schemen/OpenFormicaria/Formicaria/Inserts/Lasius_size_m.png

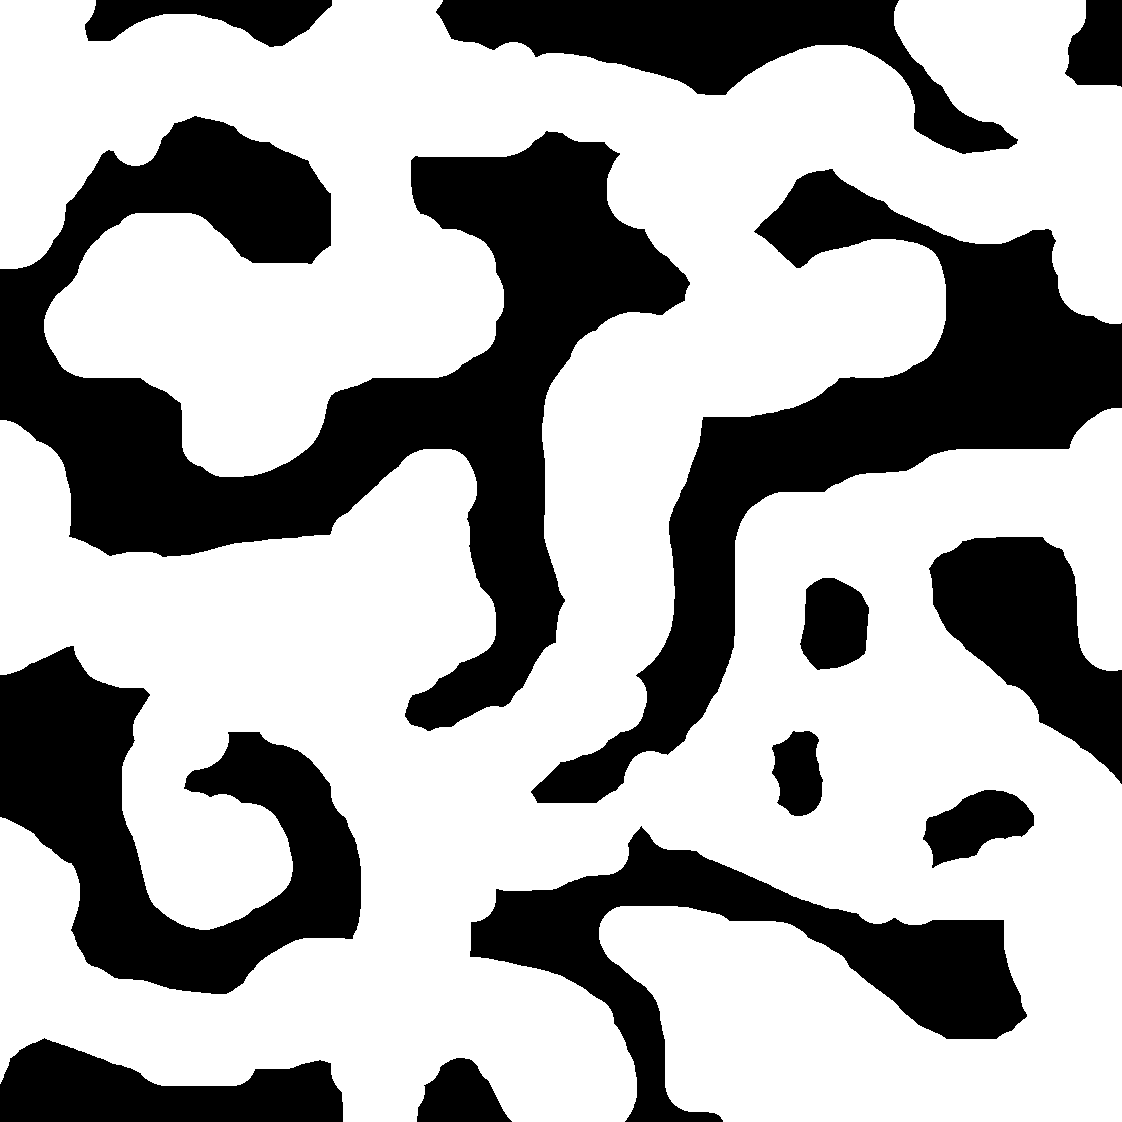
Formicaria/Inserts/Lasius_size_m.png
