schemen/OpenFormicaria/Formicaria/Inserts/Lasius_size_s.png

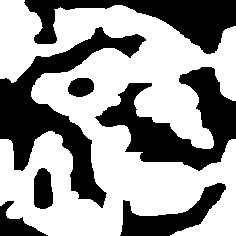
Formicaria/Inserts/Lasius_size_s.png
