schemen/OpenFormicaria/Modules/CAD/CV1/4xGateway.FCStd

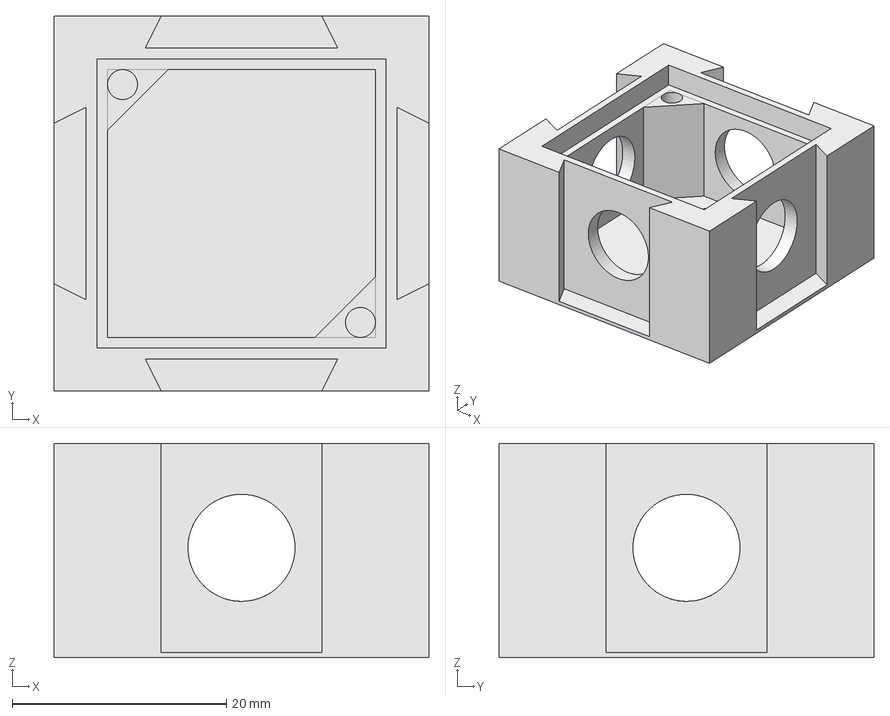
[picture p29: CAD file, 2020-11-02]
Modules/CAD/CV1/4xGateway.FCStd
35.0 x 35.0 x 20.0 mm
