schemen/OpenFormicaria/Modules/CAD/CV2/CV2_4xGateway.FCStd

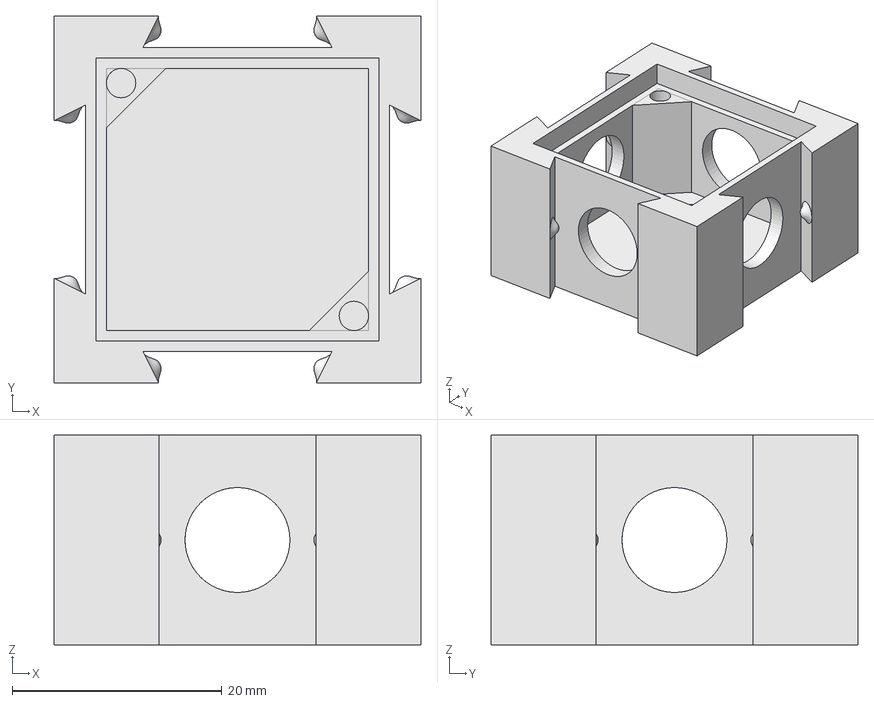
[picture p30: CAD file, 2020-11-02]
Modules/CAD/CV2/CV2_4xGateway.FCStd
35.0 x 35.0 x 20.0 mm
