schemen/OpenFormicaria/Modules/CAD/Portal_FeederLid.FCStd

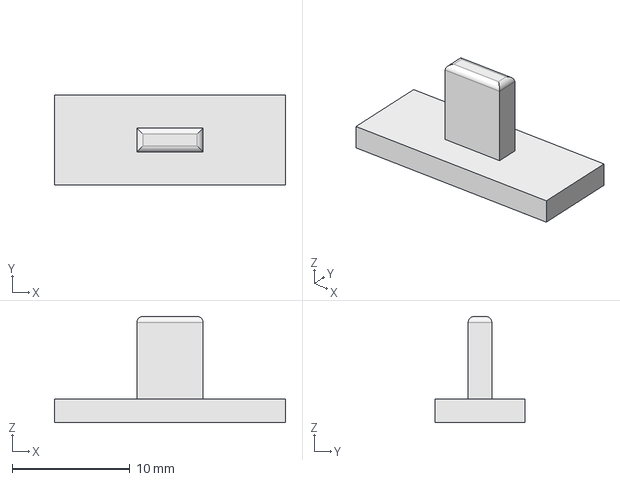
[picture p31: CAD file, 2020-10-29]
Modules/CAD/Portal_FeederLid.FCStd
19.6 x 7.60 x 9.00 mm
