schemen/OpenFormicaria/Connectors/CAD/Connector Version 2/V2_Connector_90deg_tube_12mm.FCStd

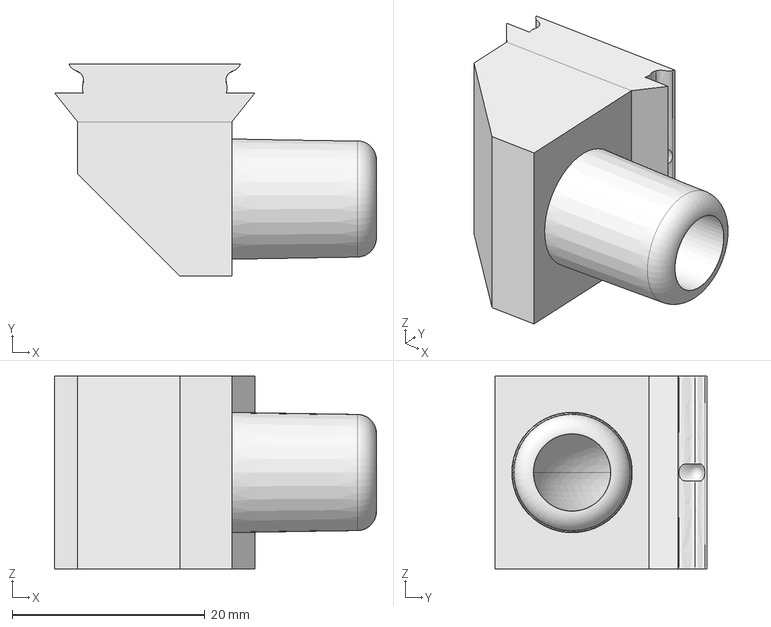
[picture p32: CAD file, 2020-11-05]
Connectors/CAD/Connector Version 2/V2_Connector_90deg_tube_12mm.FCStd
33.4 x 22.0 x 20.0 mm
