schemen/OpenFormicaria/Formicaria/CAD/Formicarium_Lid_S.FCStd

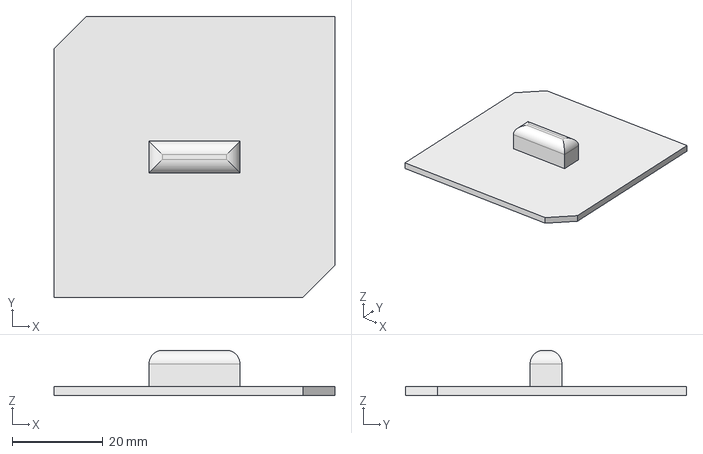
[picture p33: CAD file, 2020-11-02]
Formicaria/CAD/Formicarium_Lid_S.FCStd
61.8 x 61.8 x 10.0 mm
