schemen/OpenFormicaria/Formicaria/STL/CV1/OF_Formicarium_Lasius_M.stl

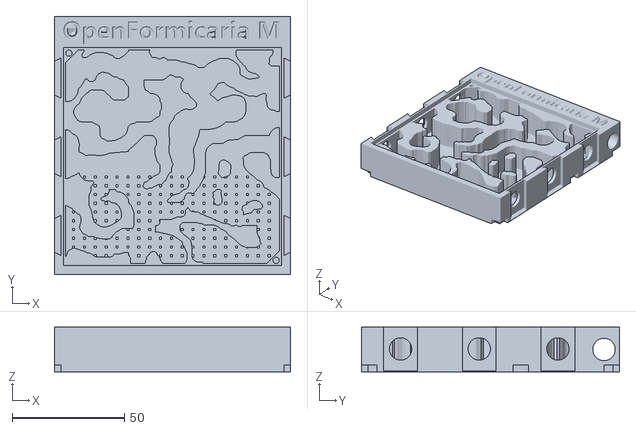
[picture p34: CAD file, 2020-11-02]
Formicaria/STL/CV1/OF_Formicarium_Lasius_M.stl
105.0 x 115.0 x 20.0
