schemen/OpenFormicaria/Formicaria/STL/CV2/CV2_OF_Formicarium_Lasius_S.stl

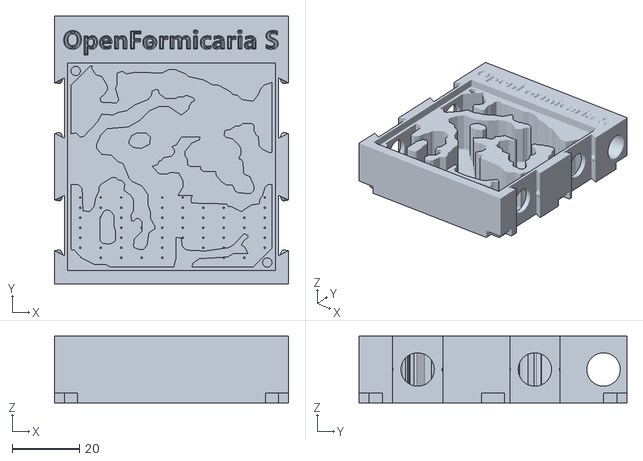
[picture p35: CAD file, 2020-11-05]
Formicaria/STL/CV2/CV2_OF_Formicarium_Lasius_S.stl
70.0 x 80.0 x 20.0
