schemen/OpenFormicaria/Modules/CAD/CV1/Portal.FCStd

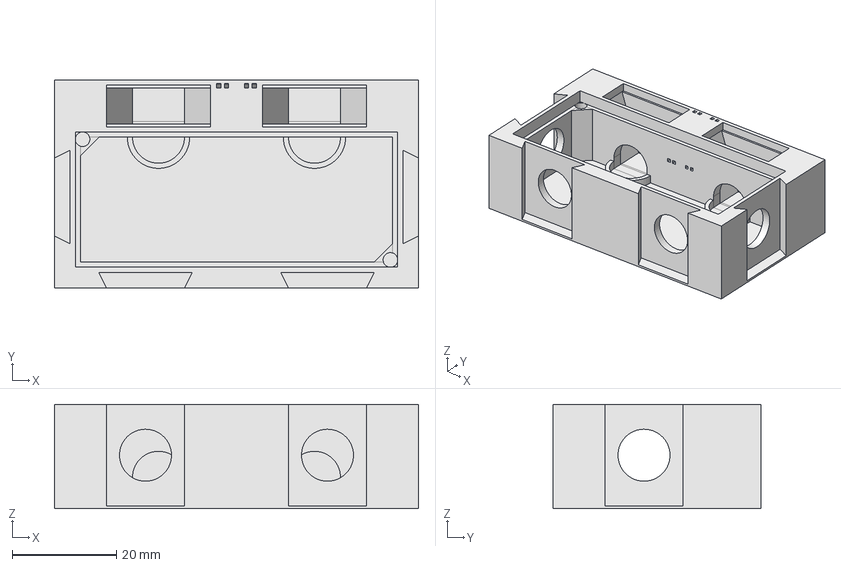
[picture p36: CAD file, 2020-10-29]
Modules/CAD/CV1/Portal.FCStd
70.0 x 40.0 x 20.0 mm
