schemen/OpenFormicaria/Connectors/CAD/Connector Version 2/V2_Connector.FCStd

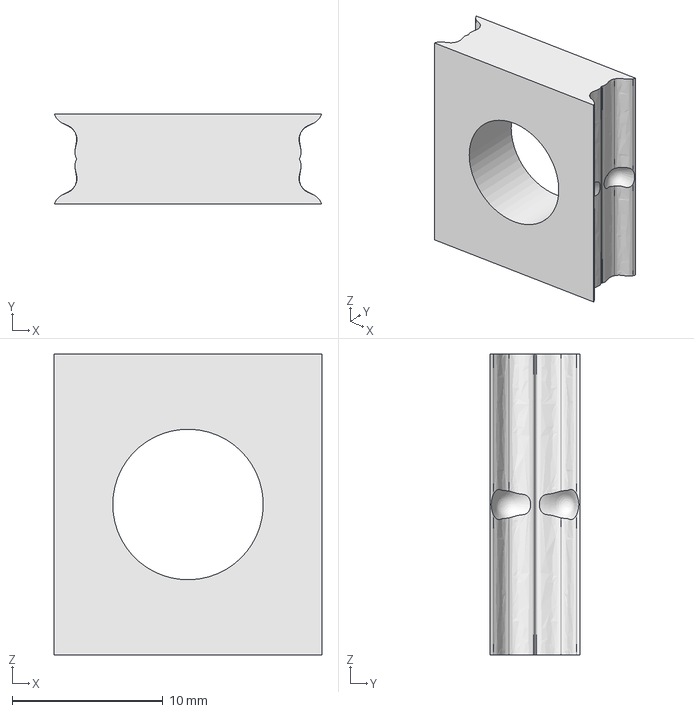
[picture p37: CAD file, 2020-11-02]
Connectors/CAD/Connector Version 2/V2_Connector.FCStd
17.8 x 6.00 x 20.0 mm
