schemen/OpenFormicaria/Formicaria/CAD/Formicarium_basin_S.FCStd

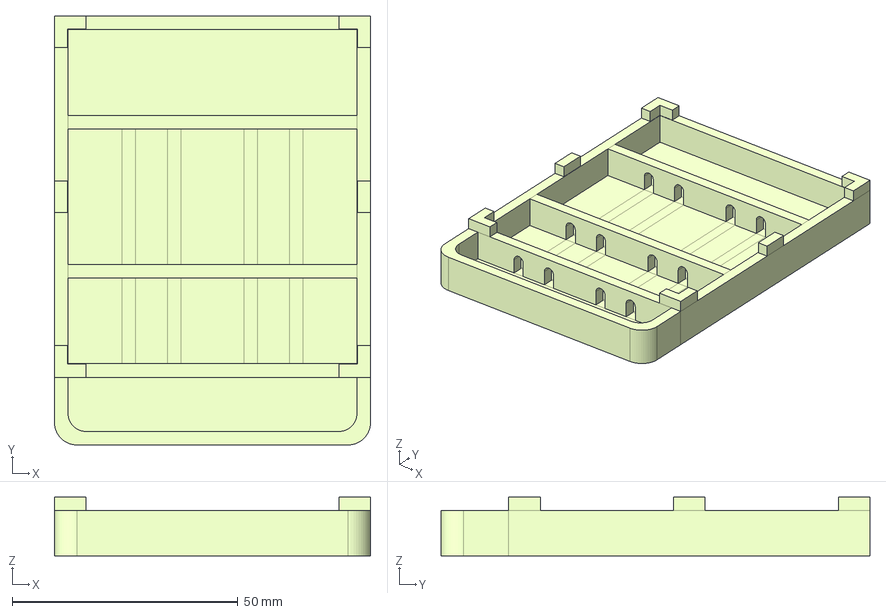
[picture p38: CAD file, 2020-10-29]
Formicaria/CAD/Formicarium_basin_S.FCStd
70.0 x 95.0 x 13.0 mm
