schemen/OpenFormicaria/Connectors/CAD/Connector Version 2/V2_Seperator.FCStd

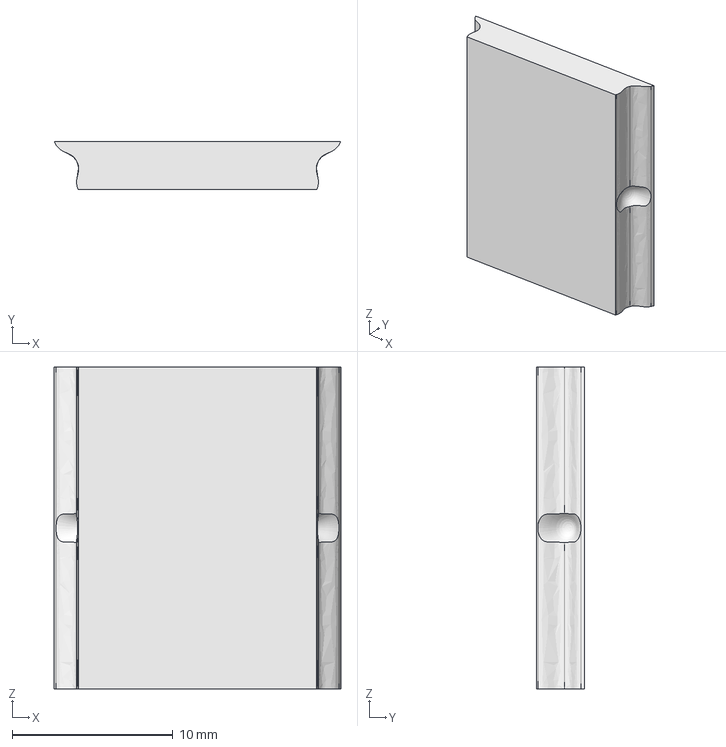
[picture p39: CAD file, 2020-11-02]
Connectors/CAD/Connector Version 2/V2_Seperator.FCStd
17.8 x 3.00 x 20.0 mm
