schemen/OpenFormicaria/Connectors/CAD/Connector Version 2/V2_Connector_tube10mm.FCStd

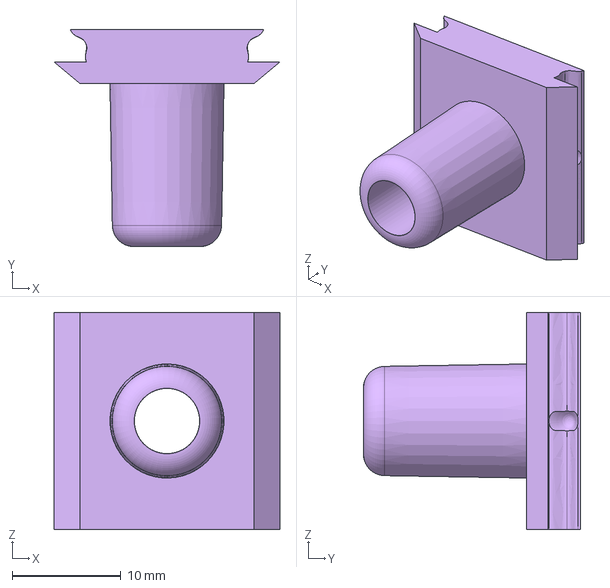
[picture p40: CAD file, 2020-11-02]
Connectors/CAD/Connector Version 2/V2_Connector_tube10mm.FCStd
20.8 x 20.0 x 20.0 mm
