schemen/OpenFormicaria/Connectors/CAD/Connector Version 2/V2_Connector_Raiser.FCStd

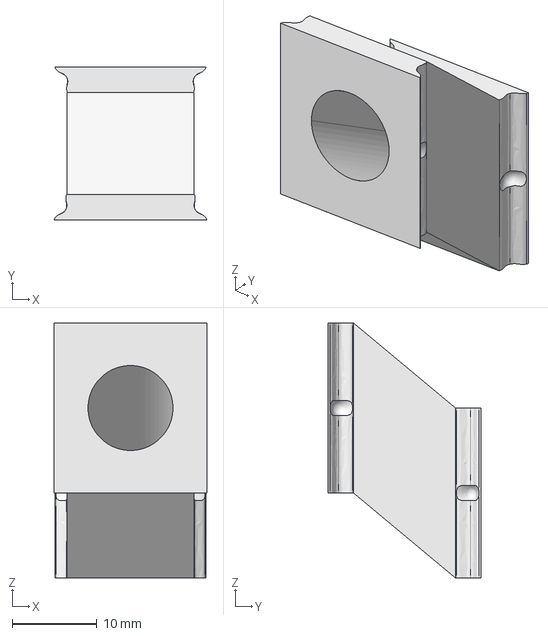
[picture p42: CAD file, 2020-11-02]
Connectors/CAD/Connector Version 2/V2_Connector_Raiser.FCStd
18.0 x 18.0 x 30.0 mm
