schemen/OpenFormicaria/Connectors/CAD/Connector Version 2/V2_Connector_tube14mm.FCStd

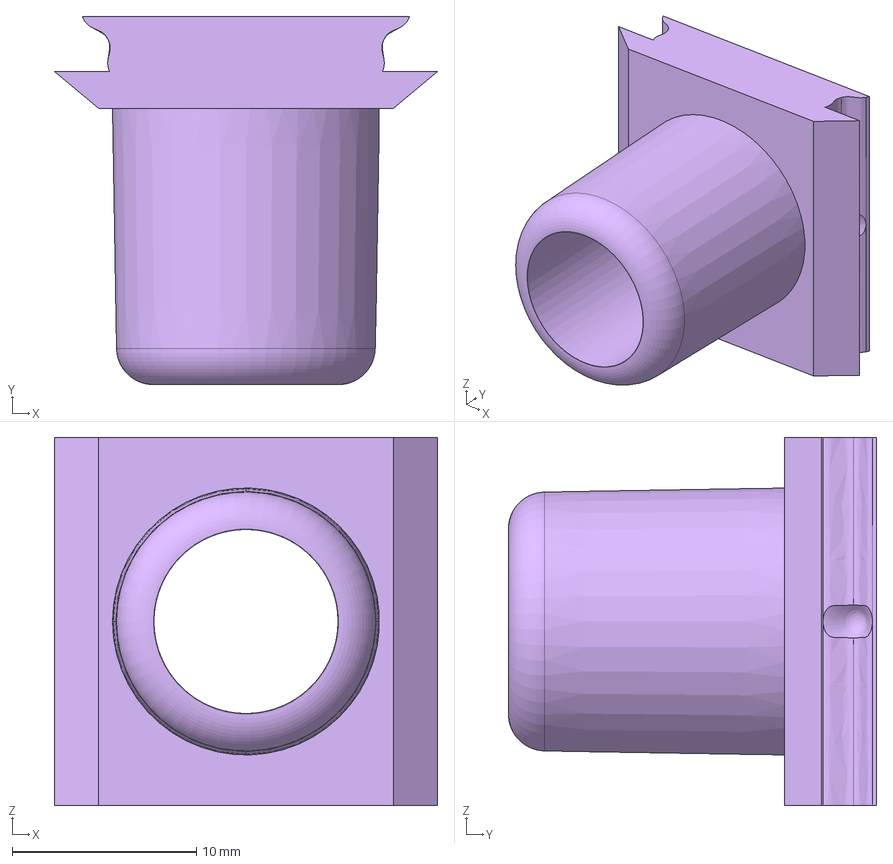
[picture p43: CAD file, 2020-11-02]
Connectors/CAD/Connector Version 2/V2_Connector_tube14mm.FCStd
20.8 x 20.0 x 20.0 mm
