schemen/OpenFormicaria/Connectors/CAD/Connector Version 2/V2_Blocker_Endpoint.FCStd

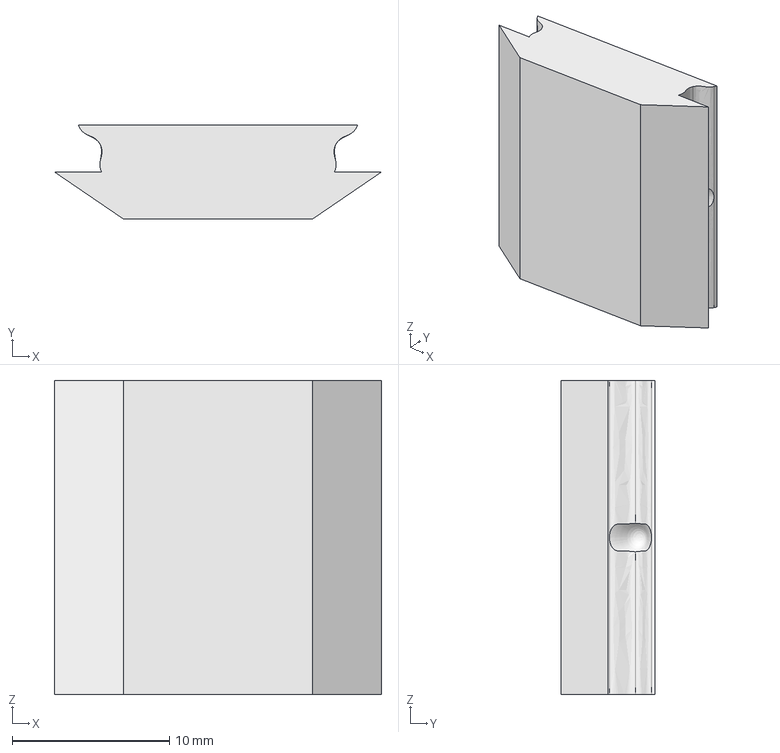
[picture p44: CAD file, 2020-11-02]
Connectors/CAD/Connector Version 2/V2_Blocker_Endpoint.FCStd
20.8 x 6.00 x 20.0 mm
