schemen/OpenFormicaria/Measurements/Connector Gate Measurements.png

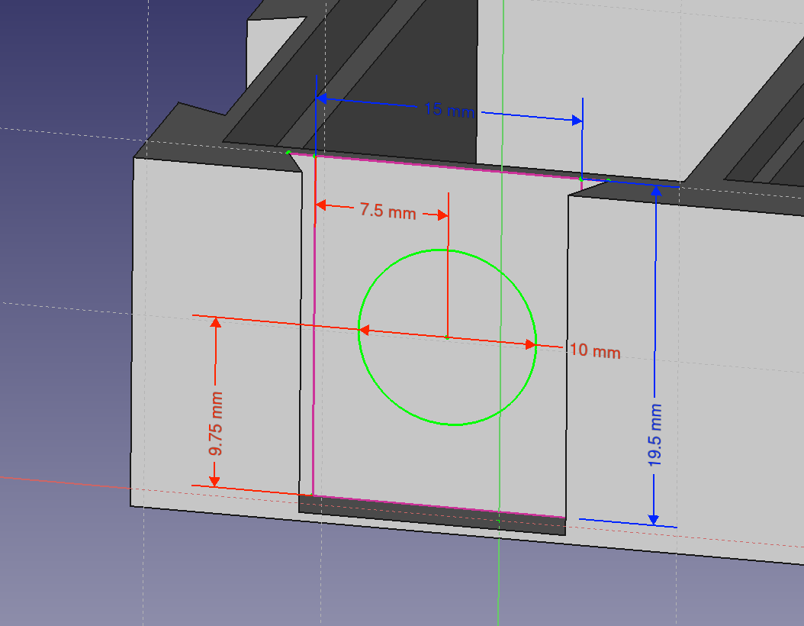
Measurements/Connector Gate Measurements.png
