schemen/OpenFormicaria/Measurements/Connector Measurements.png

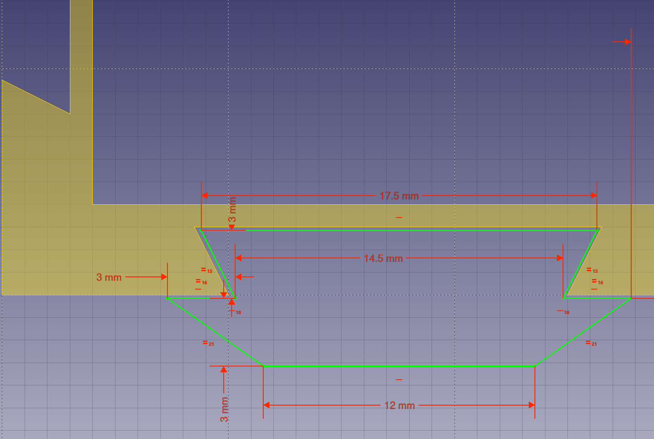
Measurements/Connector Measurements.png
